jh83/WordClock/staticScreens.h

#include "settings.h"
#define NUM_LEDS 140
static WS2812 leds;
static Pixel_t pixels[NUM_LEDS];

//int settings.dimLevel = 25; // Set the LED dim level from 0-100 %
//int settings.dimLevel;

int godJul[] =
{
  0x000000, 0x000000, 0x000000, 0x000000, 0x000000, 0x000000, 0x000000, 0x000000, 0x000000, 0x000000, 0x000000, 0x000000, 0x000000, 0xFF0000,
  0x000000, 0x000000, 0x000000, 0x000000, 0x000000, 0x000000, 0x000000, 0x000000, 0x000000, 0x000000, 0x000000, 0x000000, 0x000000, 0xFF0000,
  0x000000, 0x000000, 0x000000, 0x000000, 0x000000, 0x000000, 0x000000, 0x000000, 0x000000, 0x000000, 0x000000, 0x000000, 0x000000, 0xFF0000,
  0x000000, 0x000000, 0x000000, 0x000000, 0x000000, 0x000000, 0x000000, 0x000000, 0x000000, 0x000000, 0x000000, 0x000000, 0x000000, 0x000000,
  0x000000, 0x000000, 0x000000, 0x000000, 0x000000, 0x000000, 0x000000, 0x000000, 0x000000, 0x000000, 0x000000, 0x000000, 0x000000, 0xFF0000,
  0x000000, 0x000000, 0x000000, 0x000000, 0x000000, 0x000000, 0x000000, 0x000000, 0x000000, 0x000000, 0x000000, 0x000000, 0x000000, 0xFF0000,
  0x000000, 0x000000, 0x000000, 0x000000, 0x000000, 0x000000, 0x000000, 0x000000, 0x000000, 0x000000, 0x000000, 0x000000, 0x000000, 0xFF0000,
  0x000000, 0x000000, 0x000000, 0x000000, 0x000000, 0x000000, 0x000000, 0x000000, 0x000000, 0x000000, 0x000000, 0x000000, 0x000000, 0x000000,
  0x000000, 0x000000, 0x000000, 0x000000, 0x000000, 0x000000, 0x000000, 0x000000, 0x000000, 0x000000, 0x000000, 0x000000, 0x000000, 0x000000,
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

  // Add one hour when it should start saying "to" instead of "Past"
  if (currMinute >= 35 && currHour < 12)
    currHour = currHour + 1;
  else if (currMinute >= 35 && currHour == 12)
    currHour = 1;

  if (settings.showItIs == 1)
    showScreen(itIs, settings.dimLevel);

  // Show current Minute
  if (currMinute >= 0 && currMinute <= 4)
    showScreen(oclock, settings.dimLevel);
  else if (currMinute >= 5 && currMinute <= 9) {
    showScreen(fiveMinutes, settings.dimLevel);
    showScreen(minutes, settings.dimLevel);
    showScreen(past, settings.dimLevel);
  }
  else if (currMinute >= 10 && currMinute <= 14) {
    showScreen(tenMinutes, settings.dimLevel);
    showScreen(minutes, settings.dimLevel);
    showScreen(past, settings.dimLevel);
  }
  else if (currMinute >= 15 && currMinute <= 19) {
    showScreen(fifteenMinutes, settings.dimLevel);
    showScreen(past, settings.dimLevel);
  }
  else if (currMinute >= 20 && currMinute <= 24) {
    showScreen(twentyMinutes, settings.dimLevel);
    showScreen(minutes, settings.dimLevel);
    showScreen(past, settings.dimLevel);
  }
  else if (currMinute >= 25 && currMinute <= 29) {
    showScreen(twentyMinutes, settings.dimLevel);
    showScreen(fiveMinutes, settings.dimLevel);
    showScreen(minutes, settings.dimLevel);
    showScreen(past, settings.dimLevel);
  }
  else if (currMinute >= 30 && currMinute <= 34) {
    showScreen(thirtyMinutes, settings.dimLevel);
    showScreen(past, settings.dimLevel);
  }
  else if (currMinute >= 35 && currMinute <= 39) {
    showScreen(twentyMinutes, settings.dimLevel);
    showScreen(fiveMinutes, settings.dimLevel);
    showScreen(minutes, settings.dimLevel);
    showScreen(to, settings.dimLevel);
  }
  else if (currMinute >= 40 && currMinute <= 44) {
    showScreen(twentyMinutes, settings.dimLevel);
    showScreen(minutes, settings.dimLevel);
    showScreen(to, settings.dimLevel);
  }
  else if (currMinute >= 45 && currMinute <= 49) {
    showScreen(fifteenMinutes, settings.dimLevel);
    showScreen(to, settings.dimLevel);
  }
  else if (currMinute >= 50 && currMinute <= 54) {
    showScreen(tenMinutes, settings.dimLevel);
    showScreen(minutes, settings.dimLevel);
    showScreen(to, settings.dimLevel);
  }
  else if (currMinute >= 55 && currMinute <= 59) {
    showScreen(fiveMinutes, settings.dimLevel);
    showScreen(minutes, settings.dimLevel);
    showScreen(to, settings.dimLevel);
  }


  if (currHour == 1)
    showScreen(Hours1, settings.dimLevel);
  else if (currHour == 2)
    showScreen(Hours2, settings.dimLevel);
  else if (currHour == 3)
    showScreen(Hours3, settings.dimLevel);
  else if (currHour == 4)
    showScreen(Hours4, settings.dimLevel);
  else if (currHour == 5)
    showScreen(Hours5, settings.dimLevel);
  else if (currHour == 6)
    showScreen(Hours6, settings.dimLevel);
  else if (currHour == 7)
    showScreen(Hours7, settings.dimLevel);
  else if (currHour == 8)
    showScreen(Hours8, settings.dimLevel);
  else if (currHour == 9)
    showScreen(Hours9, settings.dimLevel);
  else if (currHour == 10)
    showScreen(Hours10, settings.dimLevel);
  else if (currHour == 11)
    showScreen(Hours11, settings.dimLevel);
  else if (currHour == 12)
    showScreen(Hours12, settings.dimLevel);
}

void showBirthday()
{
  int currMonth = month();
  int currDay = day();

  if (currMonth == 7 && currDay == 15)
  {
    showScreen(happyBirthday, settings.dimLevel);
    showScreen(johan, settings.dimLevel);
  }
  else if (currMonth == 4 && currDay == 16)
  {
    showScreen(happyBirthday, settings.dimLevel);
    showScreen(lisa, settings.dimLevel);
  }
}

void showChristmas()
{
  int currMonth = month();
  int currDay = day();

  if (currMonth == 12 && currDay == 24)
    showScreen(godJul, settings.dimLevel);
}

void updateDisplay()
{
  Serial.println("Updating Display");
  clearScreen(); // Clear the pixels
  showClock(); // Add the Clock
  showBirthday();
  showChristmas();

  leds.show(pixels); // Send the pixels to the display
}

void showNoWifi()
{
  clearScreen(); // Clear the pixels
  showScreen(noWifi, settings.dimLevel);
  leds.show(pixels); // Send the pixels to the display 
}

void clearDisplay()
{
  clearScreen(); // Clear the pixels
  leds.show(pixels); // Send the pixels to the display
}
